BoldingLab/BODA/img/CurrentDesign/Spot Diagram New.png

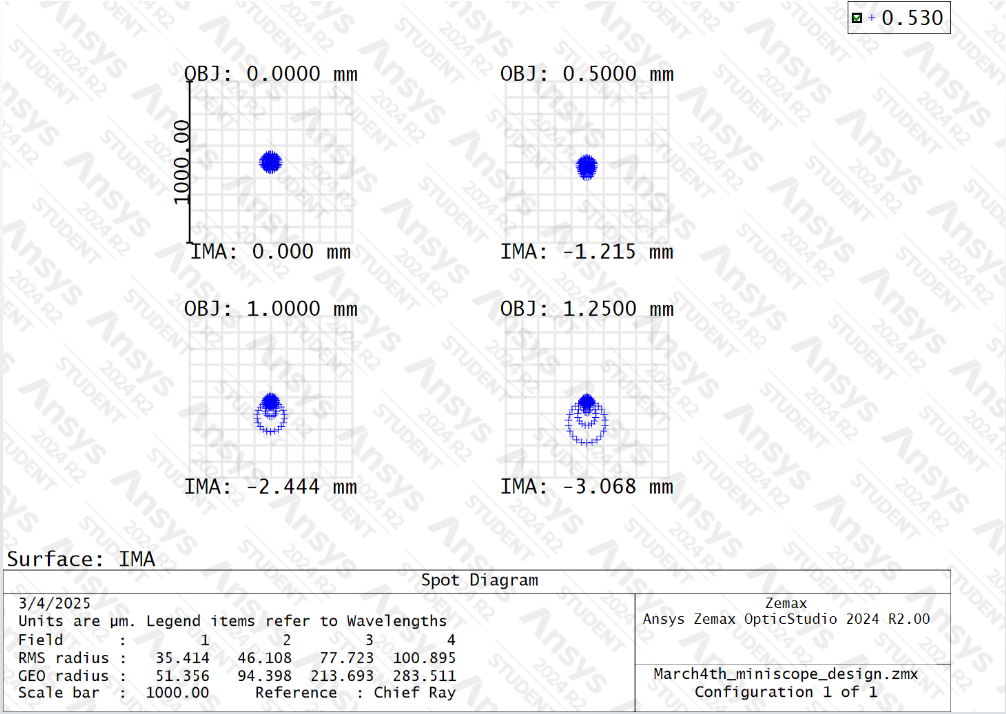
img/CurrentDesign/Spot Diagram New.png
