BoldingLab/BODA/Optical-Analysis/lens-data/59022m_plot.png

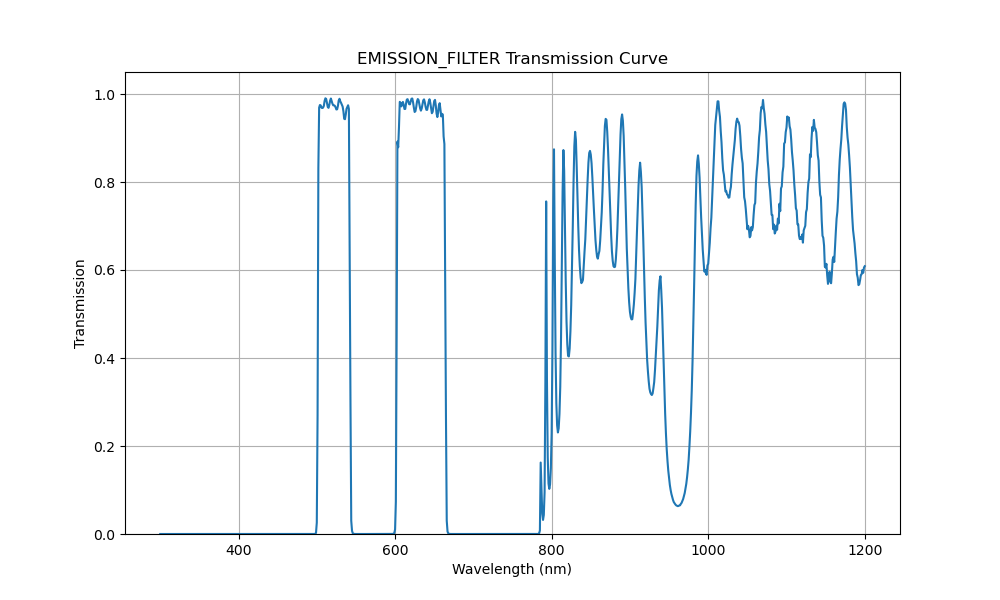
Optical-Analysis/lens-data/59022m_plot.png
