BoldingLab/BODA/Zemax/Zemax Files/Images/original_focalshift.jpg

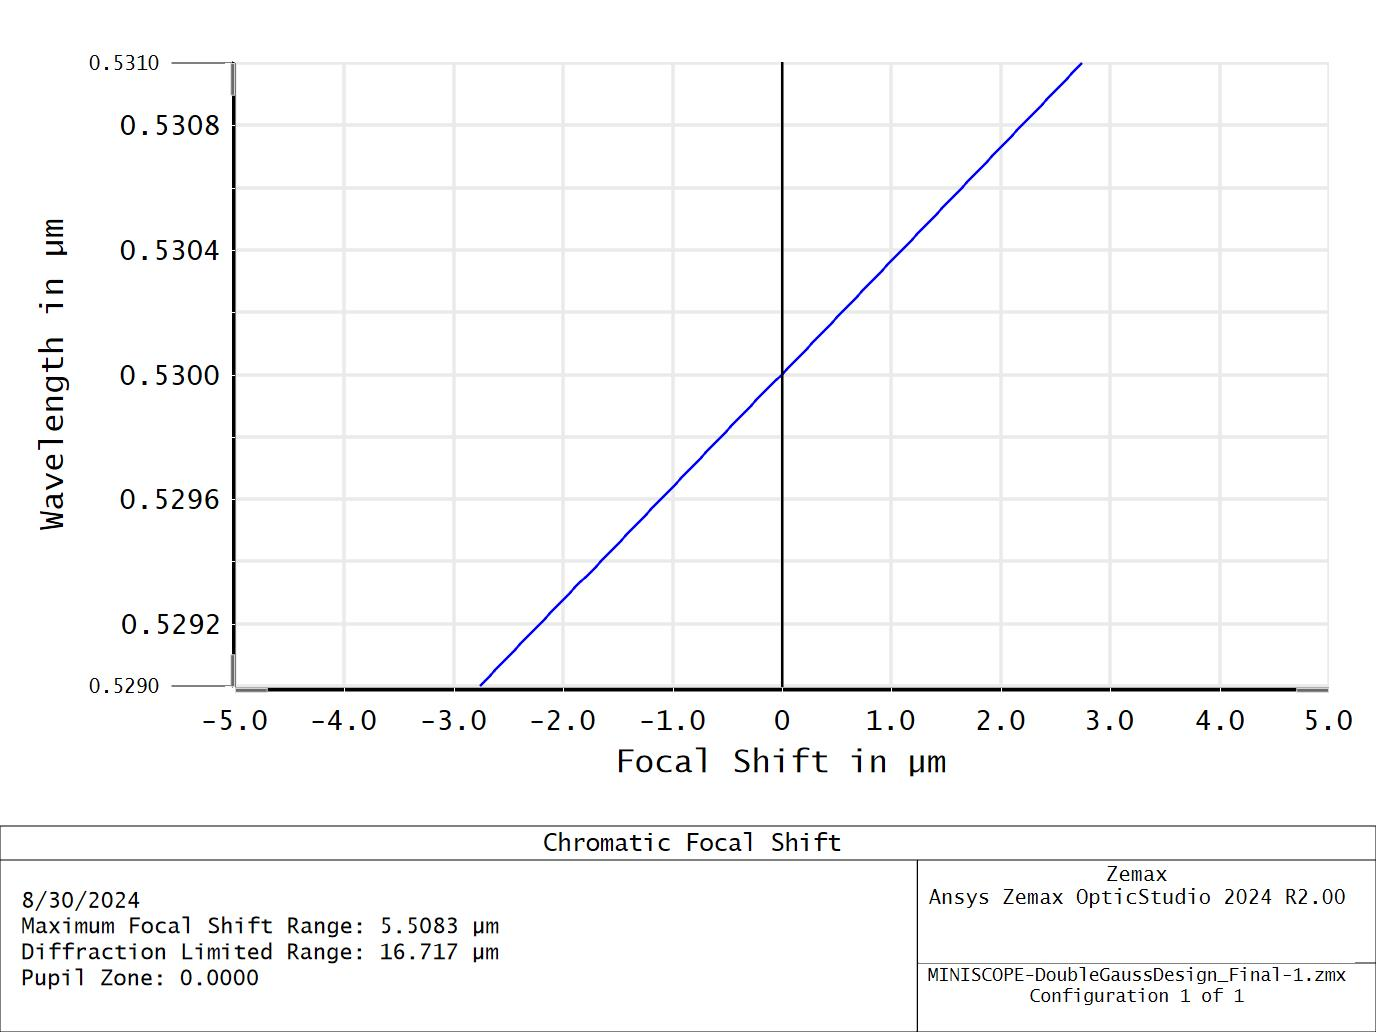
Zemax/Zemax Files/Images/original_focalshift.jpg
