BoldingLab/BODA/Zemax/Zemax Files/Images/redesign_zemax.jpg

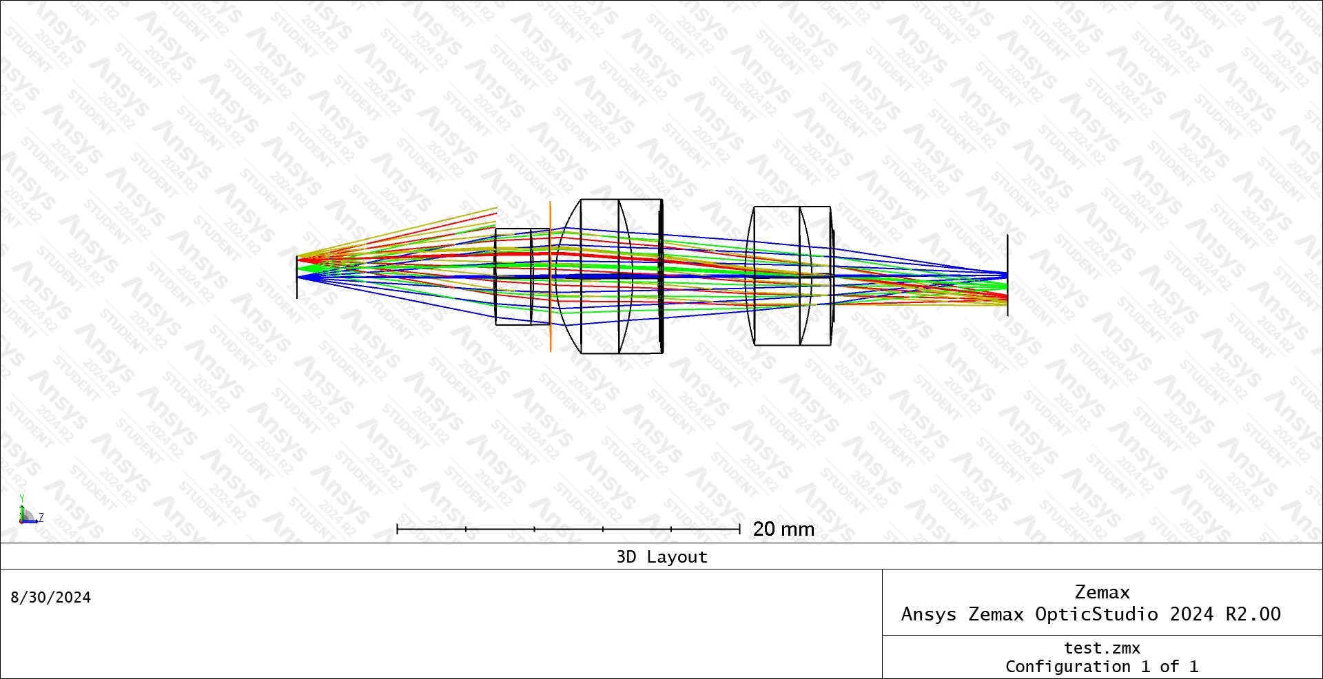
Zemax/Zemax Files/Images/redesign_zemax.jpg
